sgariba21-beep/esp32-attendance-device/images/office--04-devices.jpg

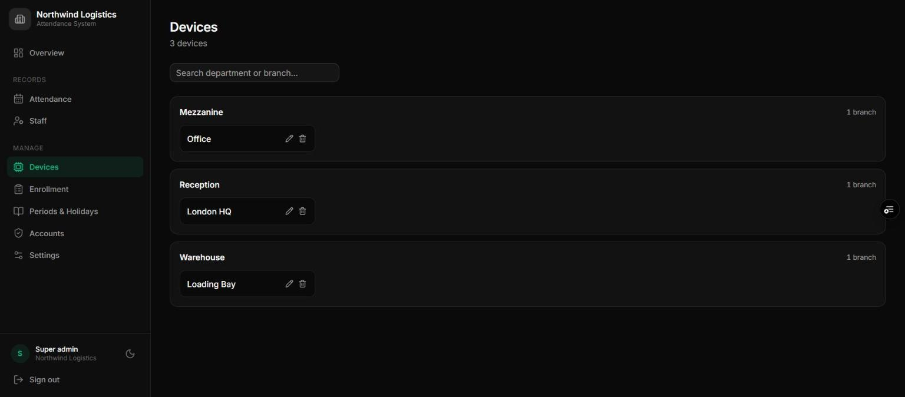
images/office--04-devices.jpg
