sgariba21-beep/esp32-attendance-device/images/office--05-enrollment.jpg

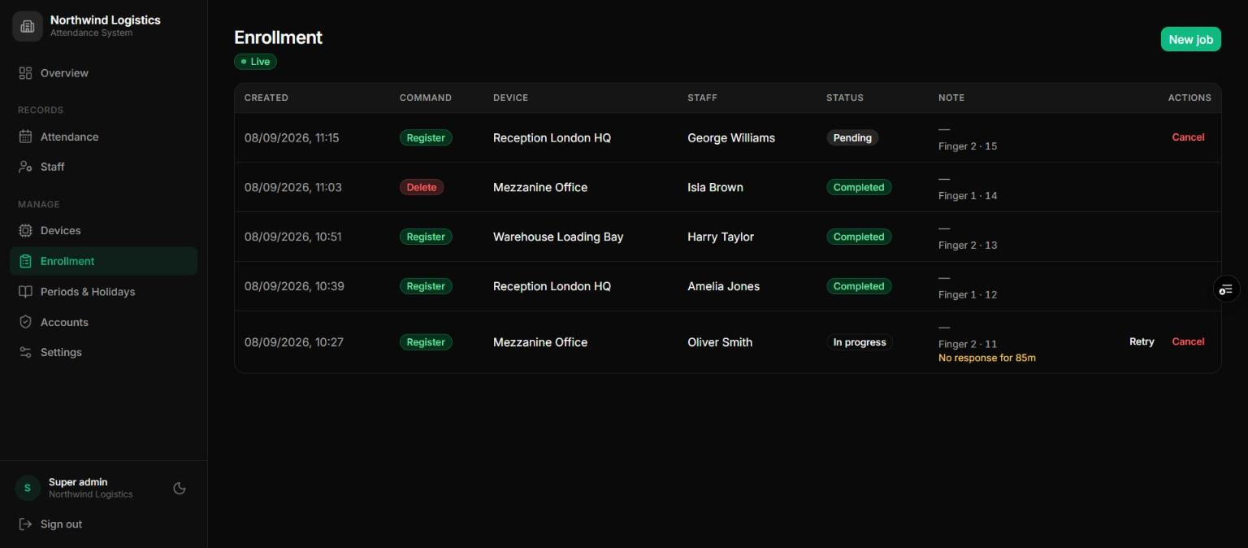
images/office--05-enrollment.jpg
