sgariba21-beep/esp32-attendance-device/images/office--07-holidays.jpg

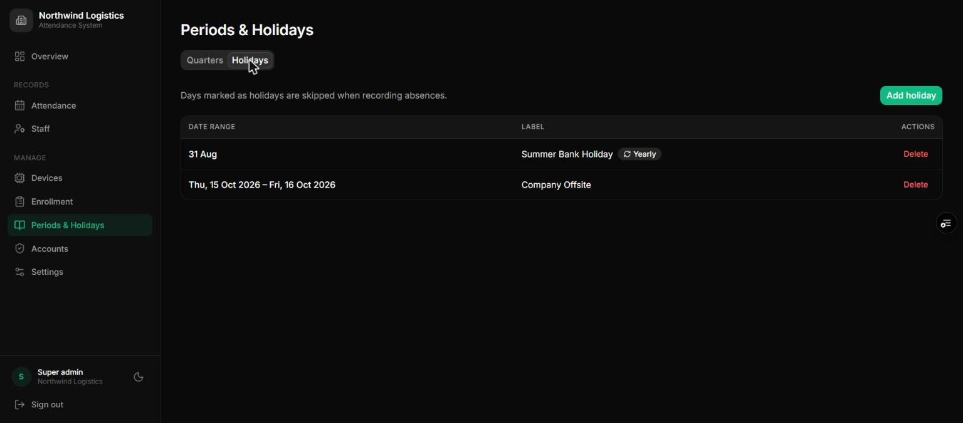
images/office--07-holidays.jpg
