sgariba21-beep/esp32-attendance-device/images/office--08-accounts.jpg

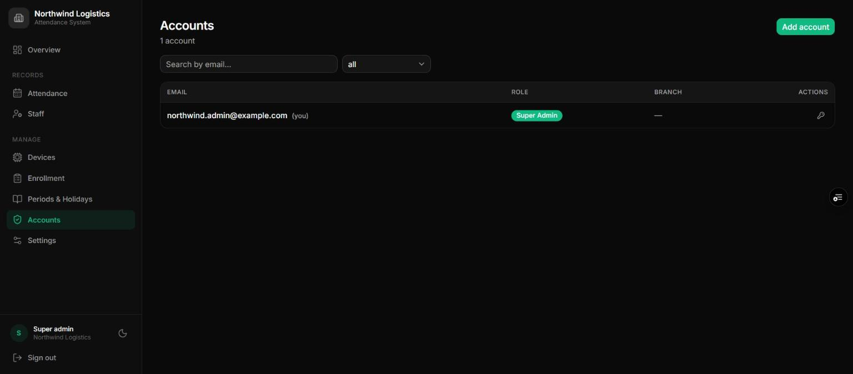
images/office--08-accounts.jpg
