sgariba21-beep/esp32-attendance-device/images/school--04-teachers.jpg

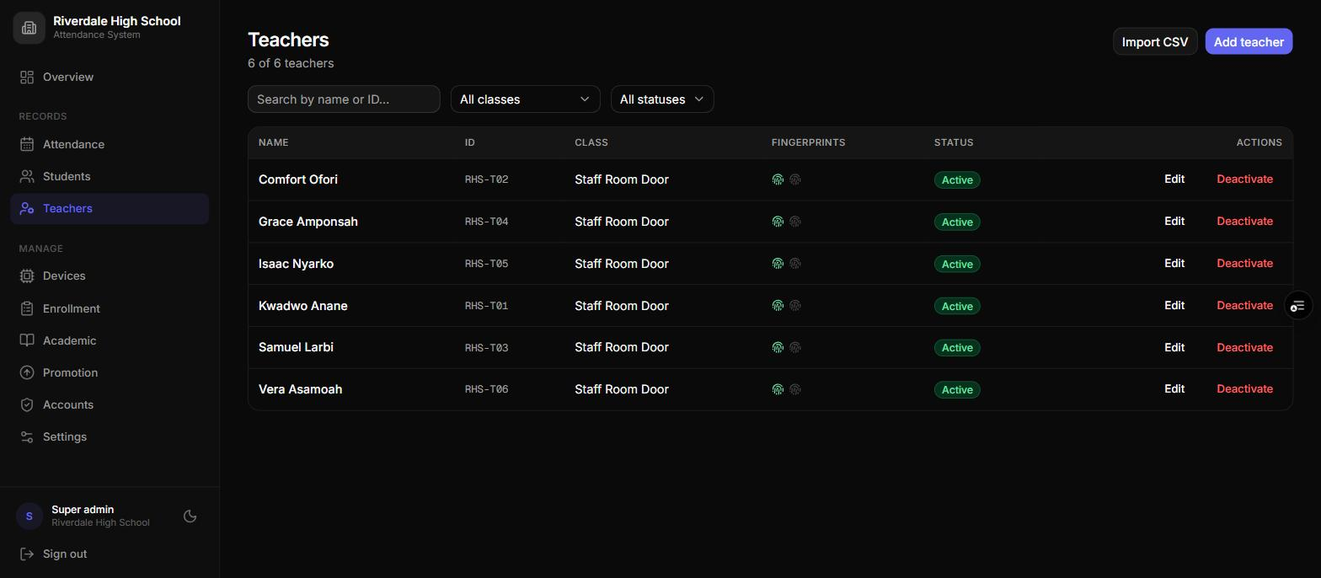
images/school--04-teachers.jpg
