sgariba21-beep/esp32-attendance-device/images/school--09-promotion.jpg

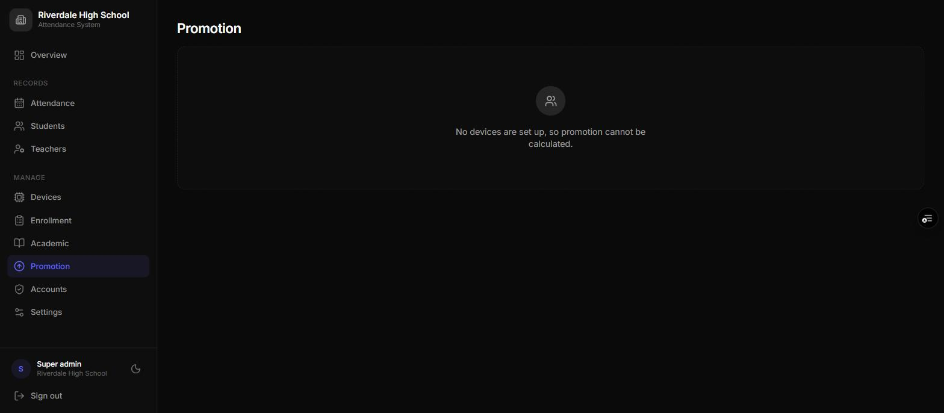
images/school--09-promotion.jpg
