sgariba21-beep/esp32-attendance-device/images/shop--02-attendance.jpg

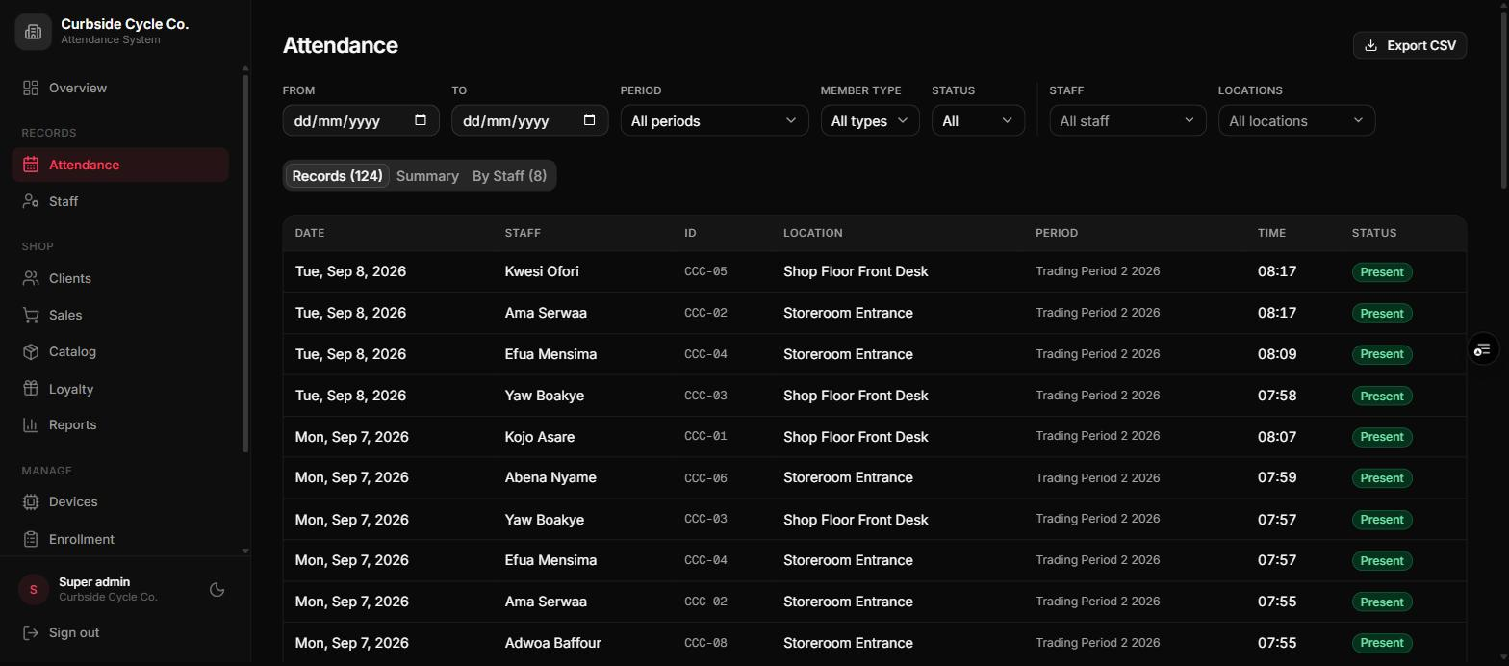
images/shop--02-attendance.jpg
