sgariba21-beep/esp32-attendance-device/images/shop--03-staff.jpg

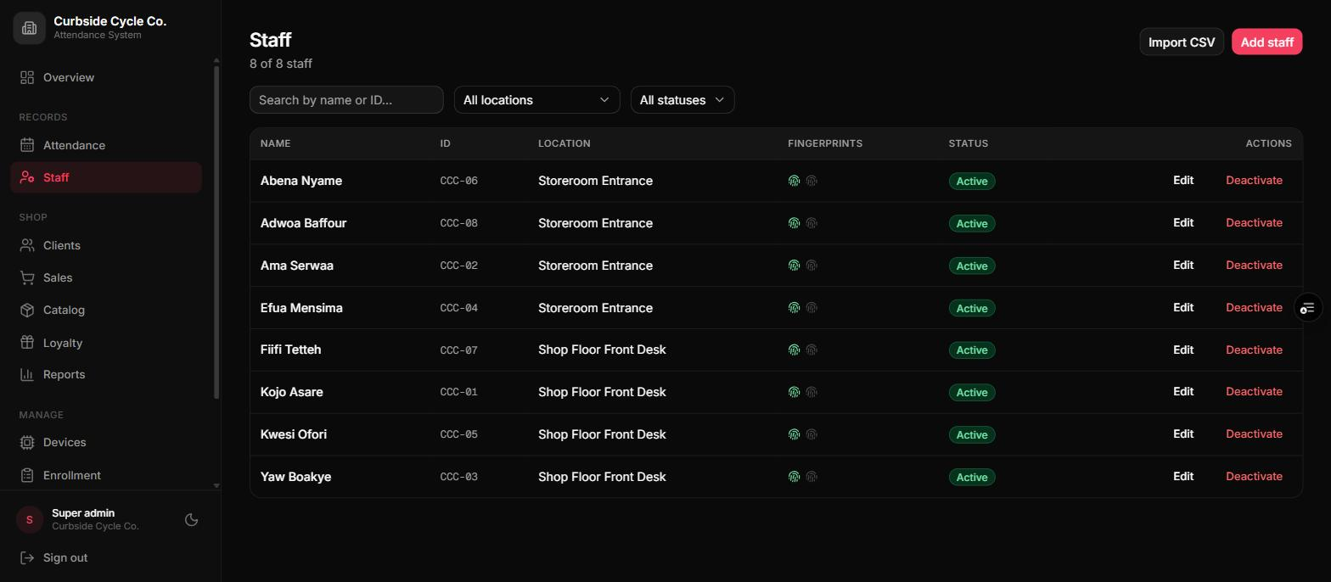
images/shop--03-staff.jpg
