sgariba21-beep/esp32-attendance-device/images/shop--07-catalog-services.jpg

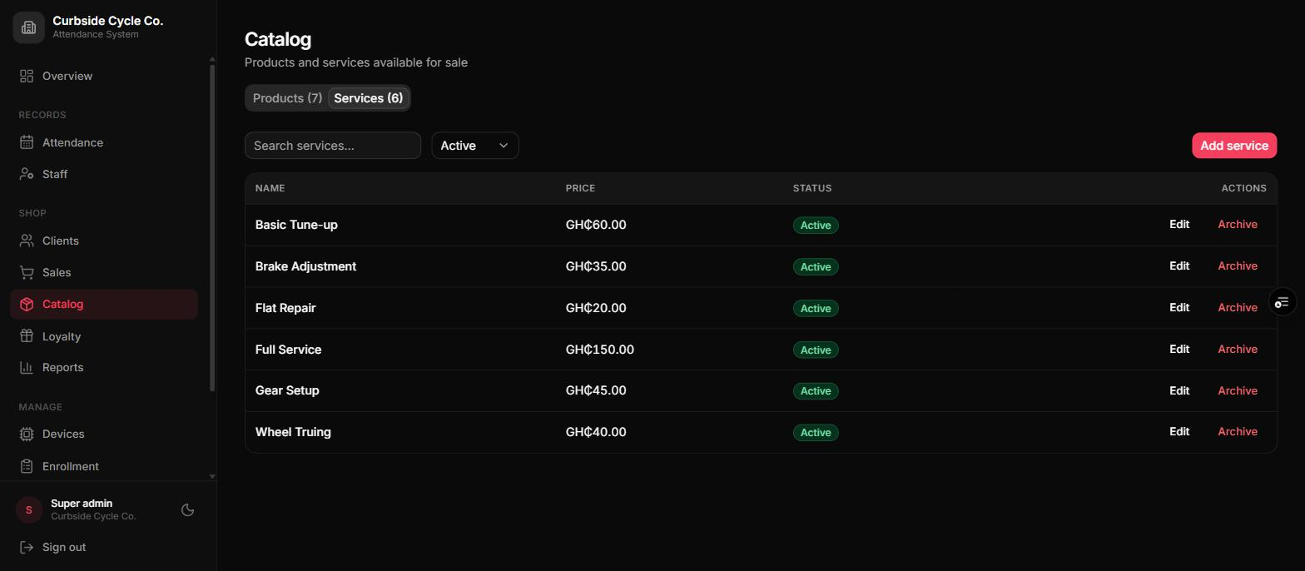
images/shop--07-catalog-services.jpg
