sgariba21-beep/esp32-attendance-device/images/shop--14-devices.jpg

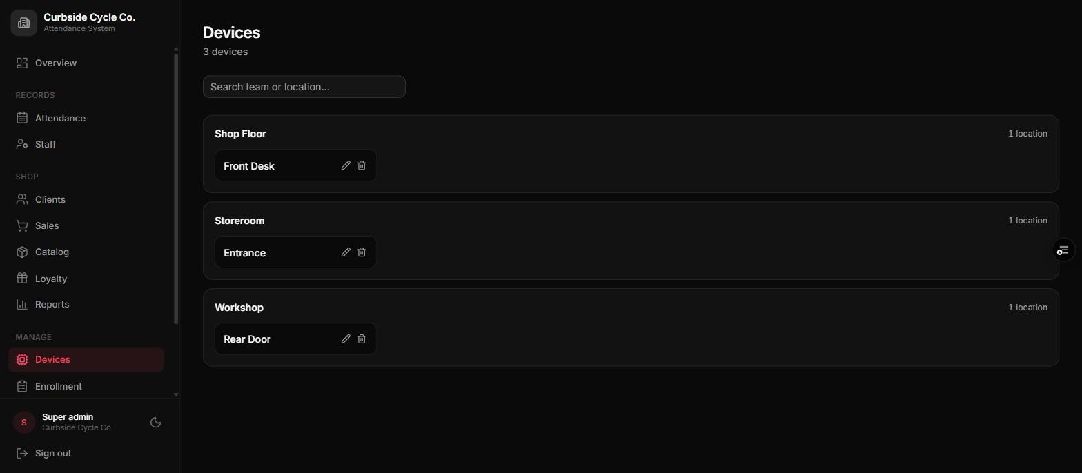
images/shop--14-devices.jpg
