sgariba21-beep/esp32-attendance-device/images/shop--15-enrollment.jpg

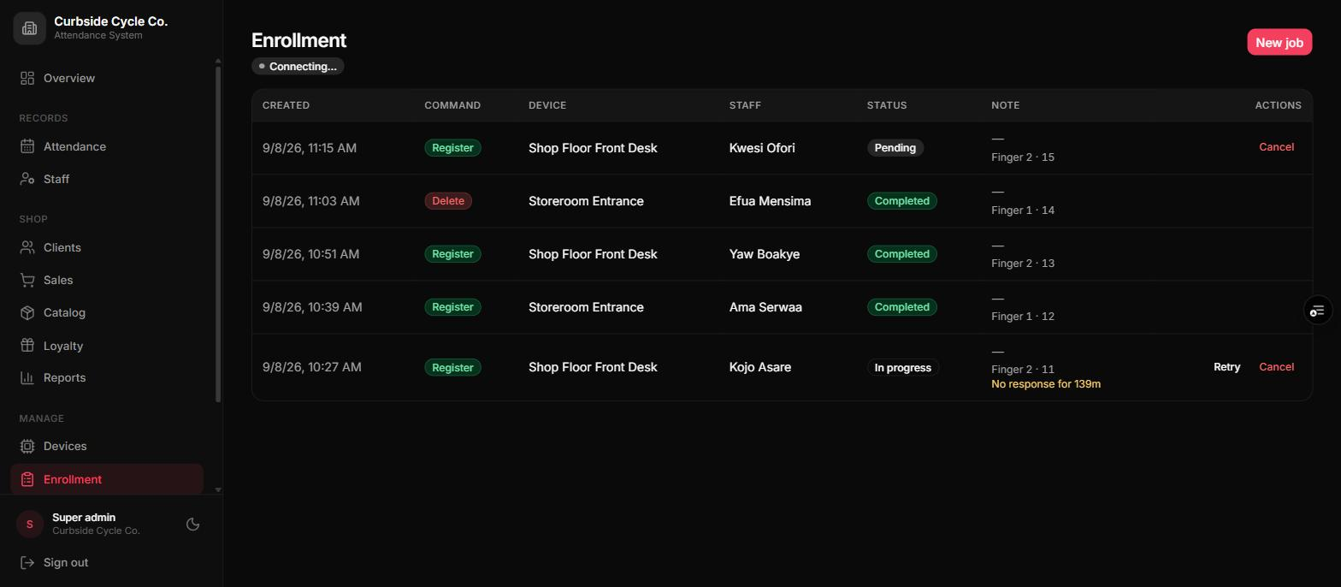
images/shop--15-enrollment.jpg
