sgariba21-beep/esp32-attendance-device/images/shop--09-loyalty-history.jpg

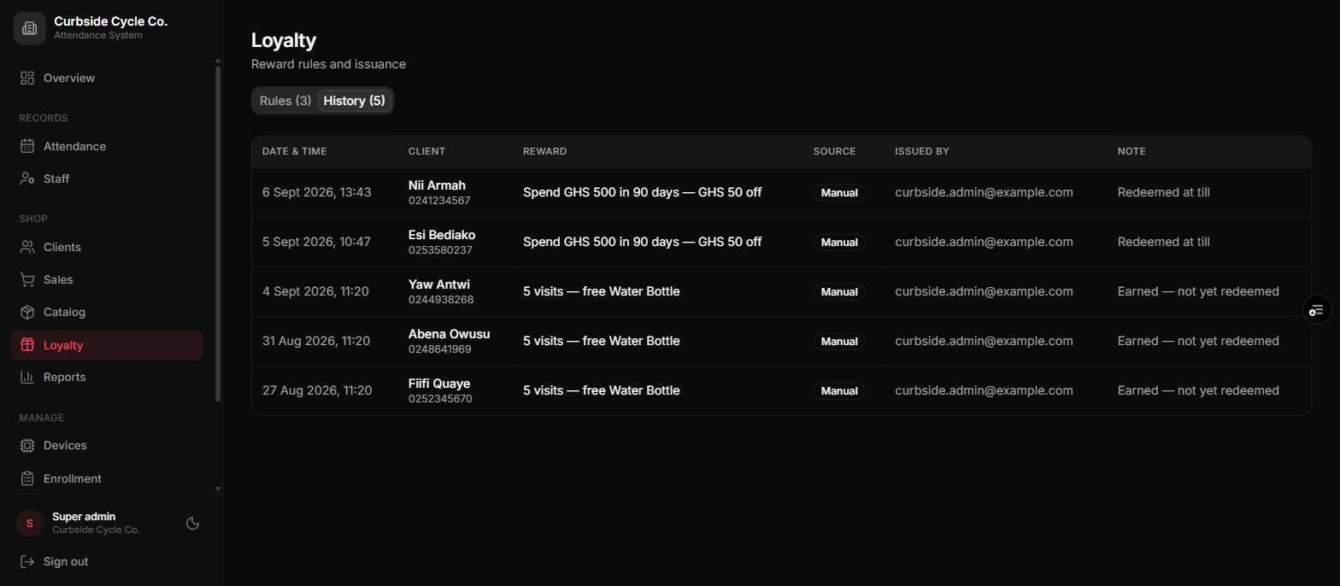
images/shop--09-loyalty-history.jpg
