sgariba21-beep/esp32-attendance-device/firmware/ClassAttendance_Current_RTC/certs.h

#pragma once
// =====================================================================
// certs.h  —  TLS root CA bundle for certificate validation (C4)
// =====================================================================
// Fetched 2026-06-15 from live servers via PowerShell X509Chain.
// Each host's intermediate AND root are included so mbedTLS can verify
// the chain regardless of whether the server sends the intermediate.
//
// Supabase (lxpemewonievaazboyez.supabase.co)
//   leaf -> WE1 (Google Trust Services) -> GlobalSign ECC Root CA R4
//
// GitHub API (api.github.com)
//   leaf -> Sectigo Public Server Auth CA DV E36 -> Sectigo Root E46
//
// GitHub CDN (objects.githubusercontent.com)
//   leaf -> R12 (Let's Encrypt) -> ISRG Root X1
//   ISRG Root X1 is sufficient; Let's Encrypt servers send R12 in-handshake.
//
// Refresh this file if any of these CAs rotate.
// =====================================================================

const char* ROOT_CA_BUNDLE = R"CERT(
-----BEGIN CERTIFICATE-----
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
-----END CERTIFICATE-----
-----BEGIN CERTIFICATE-----
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
-----END CERTIFICATE-----
-----BEGIN CERTIFICATE-----
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
NqdV
-----END CERTIFICATE-----
-----BEGIN CERTIFICATE-----
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
-----END CERTIFICATE-----
-----BEGIN CERTIFICATE-----
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
-----END CERTIFICATE-----
)CERT";
